daifukusensei/nikon-d300-d700-gps-logger/pcb/images/Project_Neptune_PCB_populated_top.JPG

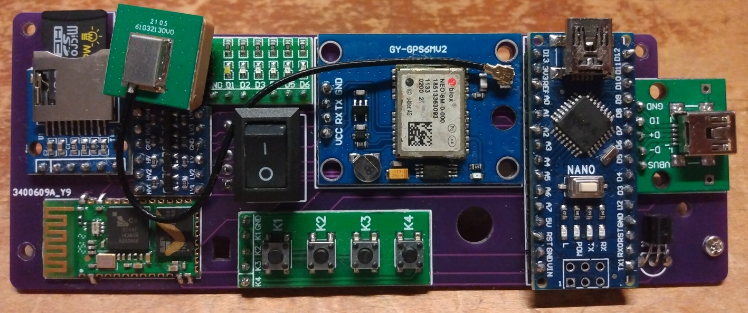
pcb/images/Project_Neptune_PCB_populated_top.JPG
